tipith/rpiz-lowpower-mobo/attiny_power_manager/src/pmtypes.h

#pragma once

#define I2C_ADDR 8

#define RPI_SHUTDOWN_TIMEOUT_MS 300000
#define RPI_POWERON_PROHIBIT_MS 10000

enum iopin
{
    PIN_IO0 = 9,
    PIN_IO1 = 2,
    PIN_IO2 = 10,
    PIN_IO3 = 1,
    PIN_RPI_EVENT = 5,
    PIN_PWR_EN = 3,
    PIN_LED = 4,
    PIN_SCL = 7,
    PIN_SDA = 6,
    PIN_ADC_VBATT = 8,
    PIN_ADC_RPI_3V3 = 0,
};

enum i2c_reg
{
    REG_VBATT = 1,
    REG_VRPI,
    REG_STARTUP_REASON,
    REG_TEMPERATURE,
    REG_DEBUG_DATA_READ,
    REG_REQUEST_SHUTDOWN
};
